andruhon/pico-dog/kicad/pico-dog.kicad_sch

## KiCad design kicad/pico-dog.kicad_sch (2026-02-07)

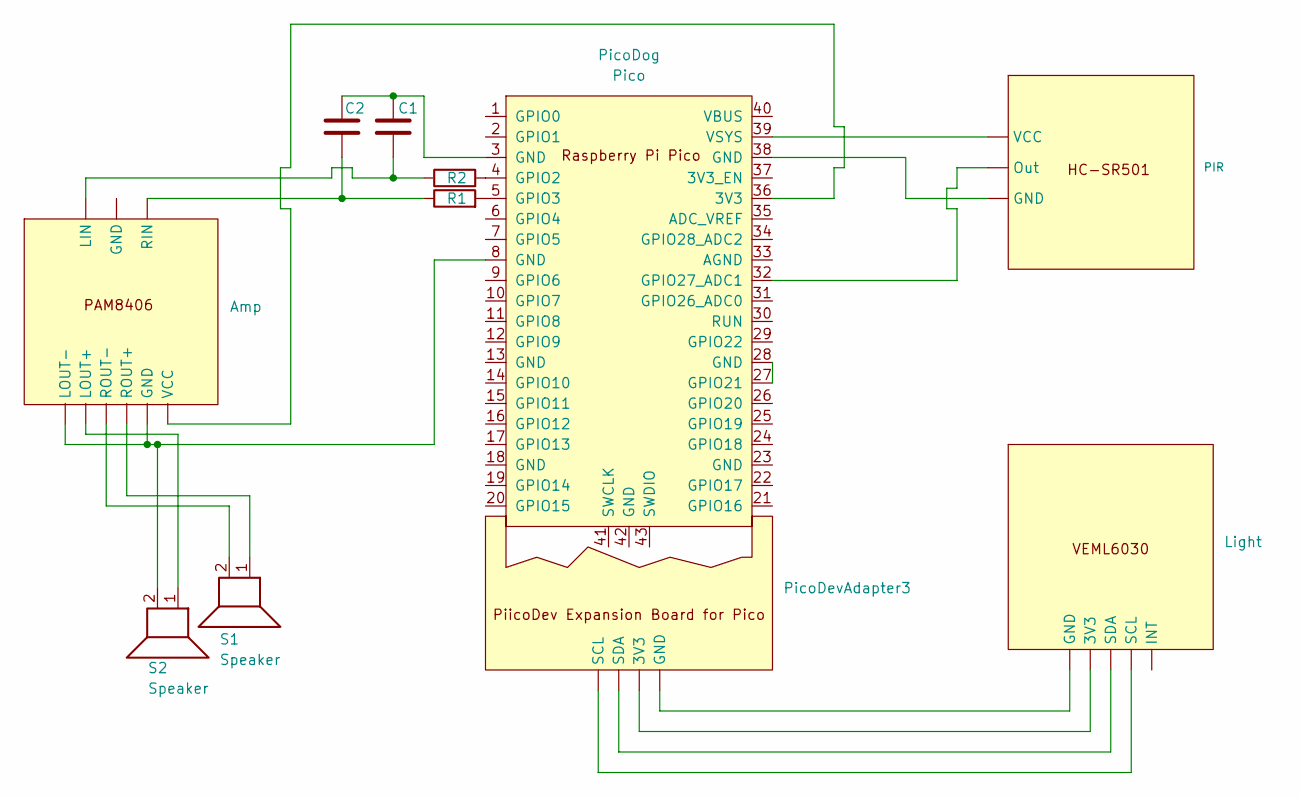
[picture p6: schematic pico-dog.kicad_sch]

Parts:
Amp: (no value)
C1, C2: C
Light: (no value)
PIR: (no value)
PicoDevAdapter1, PicoDevAdapter3: (no value)
PicoDog: Pico; RPi_Pico_SMD_TH
R1, R2: R
S1, S2: Speaker

Connections:
unnamed: Amp., C1.1, C2.1, PicoDog.8 (GND), PicoDog.36 (3V3), R1.1, R2.1, S1.1, S1.2, S2.1, S2.2
unnamed: C1.2, C2.2, PicoDog.3 (GND)
unnamed: Light., PicoDevAdapter3.
unnamed: PIR., PicoDog.32 (GPIO27_ADC1), PicoDog.38 (GND), PicoDog.39 (VSYS)
unnamed: PicoDog.4 (GPIO2), R2.2
unnamed: PicoDog.5 (GPIO3), R1.2
unnamed: PicoDog.27 (GPIO21), PicoDog.28 (GND)
